opentrv/3d-boxes/src/main/boiler_control_ssr-v0p2_rev1.scad

/*
The OpenTRV project licenses this file to you
under the Apache Licence, Version 2.0 (the "Licence");
you may not use this file except in compliance
with the Licence. You may obtain a copy of the Licence at

http://www.apache.org/licenses/LICENSE-2.0

Unless required by applicable law or agreed to in writing,
software distributed under the Licence is distributed on an
"AS IS" BASIS, WITHOUT WARRANTIES OR CONDITIONS OF ANY
KIND, either express or implied. See the Licence for the
specific language governing permissions and limitations
under the Licence.

Author(s) / Copyright (s): Bo Herrmannsen, Bruno Girin 2013
*/

include <boiler_control_ssr-v0p1_rev1-settings.scad>;
include <common.scad>;
include <bitmap.scad>;


module layer_0_0(thickness=layer_0_0_thickness) {
    difference() {
        box_base(thickness);
        box_mounting_holes(thickness);
        translate([0, box_total_length / 4, 0])
            box_wall_mount_screw_holes(thickness);
        translate([0, 0, -0.1])
            nut_recesses(nut_recess_height);
    }
}

module layer_0_5(thickness=box_layer_thickness) {
    box_spacer_layer(thickness);
}

module layer_0_1b(thickness=layer_0_1b_thickness, hole_offset_z, hole_thickness) {
    difference() {
        box_spacer_layer(thickness);
        
        translate([0, 0, hole_offset_z])
        box_outside_hole(
            wire_hole_controller_side,
            wire_hole_controller_width,
            box_wall_width + 0.1,
            wire_hole_controller_offset,
            hole_thickness
        );
        
    }
}

module layer_0() {
    difference() {
        union() {
            layer_0_0(layer_0_0_thickness);
            translate([0, 0, layer_0_0_thickness - 0.1])
                layer_0_1b(layer_0_1b_thickness, layer_0_1b_hole_offset_z, layer_0_1b_hole_thickness);
        }
        for ( hoffset = [-18 : 6 : 6] ) {
            ventilation_slit(TOP, 2, slit_thickness - 4, box_wall_width, hoffset, slit_offset_z + 2);
        }
        for ( hoffset = [0 : 6 : 18] ) {
            ventilation_slit(BOTTOM, 2, slit_thickness - 4, box_wall_width, hoffset, slit_offset_z + 2);
        }
        for ( hoffset = [-36 : 6 : 36] ) {
            ventilation_slit(RIGHT, 2, slit_thickness - 4, box_wall_width, hoffset, slit_offset_z + 2);
            ventilation_slit(LEFT, 2, slit_thickness - 4, box_wall_width, hoffset, slit_offset_z + 2);
        }
        translate ([
                wire_hole_mains_offset_x,
                -box_total_length / 2 + box_wall_width / 2,
                layer_0_0_thickness + wire_hole_mains_offset_z + wire_hole_mains_radius]) {
            rotate (a = 90, v = [1,0,0])
            cylinder (
                h = box_wall_width + 0.2,
                r=wire_hole_mains_radius,
                $fn=cylinder_resolution, center = true);
        }
    }
    for ( hoffset = [-18 : 6 : 6] ) {
        ventilation_screen(TOP, 4, 1, slit_thickness + 0.1, box_wall_width, 2, hoffset, slit_offset_z - 0.1);
    }
    for ( hoffset = [0 : 6 : 18] ) {
        ventilation_screen(BOTTOM, 4, 1, slit_thickness + 0.1, box_wall_width, 2, hoffset, slit_offset_z - 0.1);
    }
    for ( hoffset = [-36 : 6 : 36] ) {
        ventilation_screen(RIGHT, 4, 1, slit_thickness + 0.1, box_wall_width, 2, hoffset, slit_offset_z - 0.1);
        ventilation_screen(LEFT, 4, 1, slit_thickness + 0.1, box_wall_width, 2, hoffset, slit_offset_z - 0.1);
    }
}


module layer_1() {
    difference() {
        union() {
            difference() {
                box_base(layer_1_thickness);
                box_mounting_holes(layer_1_thickness);
                
                /* SSR label */
                translate([
                    -label_ssr_char_count * 3 * label_block_size,
                    led_hole_radius * 5,
                    layer_1_thickness - label_recess_depth + 0.1
                    ])
                rotate(a = -90, v = [0, 0, 1])
                    8bit_str(label_ssr_chars, label_ssr_char_count, label_block_size, label_recess_depth + 0.1);
                /* OpenTRV label */
                translate([
                    -label_opentrv_char_count * 3.5 * label_block_size,
                    -pcb_length / 4,
                    layer_1_thickness - label_recess_depth + 0.1
                    ])
                rotate(a = -90, v = [0, 0, 1])
                    8bit_str(label_opentrv_chars, label_opentrv_char_count, label_block_size, label_recess_depth + 0.1);
                /* Recesses */
                translate([0, 0, layer_1_thickness - bolt_head_recess_height])
                    nut_recesses(bolt_head_recess_height);

                /* LED hole */
                translate([0, 0, -0.1])
                cylinder (
                    h = layer_1_thickness + 0.2,
                    r = led_hole_radius + hole_fudge_factor,
                    $fn = cylinder_resolution);
            }
        }
        
    }
}

module print_layer(n) {
    if ( n == 0 ) {
        layer_0();
    }
    if ( n == 1 ) {
        layer_1();
    }
}

if(box_layout == BOX_LAYOUT_STACKED) {
    layer_0();

    translate([0, 0, layer_0_thickness + box_layout_spacing])
    layer_1();
}
if(box_layout == BOX_LAYOUT_PRINT) {
    translate([
        -(box_total_width + box_layout_spacing) / 2,
        0,
        0])
    layer_0();

    translate([
         (box_total_width + box_layout_spacing) / 2,
        0,
        0])
    layer_1();
    
    if(use_lilypads == true) {
        lilypads(2, 1, box_total_width, box_total_length);
    }
}
if(box_layout == BOX_LAYOUT_1LAYER_PRINT) {
    for ( dx = [ -(n_prints_x - 1) / 2 : (n_prints_x - 1) / 2 ] ) {
        for ( dy = [ -(n_prints_y - 1) / 2 : (n_prints_y - 1) / 2 ] ) {
            translate([
                dx * (box_total_width + box_layout_spacing),
                dy * (box_total_length + box_layout_spacing),
                0
            ])
            print_layer(layer_to_print);
        }
    }
    
    if(use_lilypads == true) {
        lilypads(n_prints_x, n_prints_y, box_total_width, box_total_length);
    }
}
