opentrv/3d-boxes/src/box_basic.scad

/*
The OpenTRV project licenses this file to you
under the Apache Licence, Version 2.0 (the "Licence");
you may not use this file except in compliance
with the Licence. You may obtain a copy of the Licence at

http://www.apache.org/licenses/LICENSE-2.0

Unless required by applicable law or agreed to in writing,
software distributed under the Licence is distributed on an
"AS IS" BASIS, WITHOUT WARRANTIES OR CONDITIONS OF ANY
KIND, either express or implied. See the Licence for the
specific language governing permissions and limitations
under the Licence.

Author(s) / Copyright (s): Bruno Girin 2013
*/

include <settings.scad>;

box_total_width = pcb_width + 2 * box_wall_width;
box_cube_width = box_total_width - 2 * box_corner_radius;
box_total_length = pcb_length + 2 * box_wall_width;
box_cube_length = box_total_length - 2 * box_corner_radius;
mounting_hole_pcb_offset = pcb_mounting_hole_to_edge + pcb_mounting_hole_radius;
mounting_hole_box_offset = box_wall_width + mounting_hole_pcb_offset;

module box_mounting_hole() {
    translate([0, 0, -0.1])
    cylinder(r = pcb_mounting_hole_radius, h = box_layer_thickness + 0.2);
}

module box_mounting_holes() {
    union() {
        translate([
            -pcb_width / 2 + mounting_hole_pcb_offset,
            -pcb_length / 2 + mounting_hole_pcb_offset,
            0])
        box_mounting_hole();
        translate([
            +pcb_width / 2 - mounting_hole_pcb_offset,
            -pcb_length / 2 + mounting_hole_pcb_offset,
            0])
        box_mounting_hole();
        translate([
            +pcb_width / 2 - mounting_hole_pcb_offset,
            +pcb_length / 2 - mounting_hole_pcb_offset,
            0])
        box_mounting_hole();
        translate([
            -pcb_width / 2 + mounting_hole_pcb_offset,
            +pcb_length / 2 - mounting_hole_pcb_offset,
            0])
        box_mounting_hole();
    }
}

module box_mounting_hole_surround() {
    hull_cube_side = box_layer_thickness - box_corner_radius;
    surround_radius = pcb_mounting_hole_radius + pcb_mounting_hole_max_padding;
    hull() {
        cylinder(r = surround_radius,
            h = box_layer_thickness);
        translate([mounting_hole_pcb_offset, -surround_radius, 0])
            cube(size = [hull_cube_side, hull_cube_side, box_layer_thickness]);
        translate([-surround_radius, mounting_hole_pcb_offset, 0])
            cube(size = [hull_cube_side, hull_cube_side, box_layer_thickness]);
        translate([mounting_hole_pcb_offset, mounting_hole_pcb_offset, 0])
            cube(size = [hull_cube_side, hull_cube_side, box_layer_thickness]);
    }
}

module box_mounting_hole_surrounds() {
    union() {
        translate([
            -pcb_width / 2 + mounting_hole_pcb_offset,
            -pcb_length / 2 + mounting_hole_pcb_offset,
            0])
        rotate(a = 180, v = [0, 0, 1])
        box_mounting_hole_surround();
        translate([
            +pcb_width / 2 - mounting_hole_pcb_offset,
            -pcb_length / 2 + mounting_hole_pcb_offset,
            0])
        rotate(a = -90, v = [0, 0, 1])
        box_mounting_hole_surround();
        translate([
            +pcb_width / 2 - mounting_hole_pcb_offset,
            +pcb_length / 2 - mounting_hole_pcb_offset,
            0])
        box_mounting_hole_surround();
        translate([
            -pcb_width / 2 + mounting_hole_pcb_offset,
            +pcb_length / 2 - mounting_hole_pcb_offset,
            0])
        rotate(a = 90, v = [0, 0, 1])
        box_mounting_hole_surround();
    }
}

module box_base() {
    hull() {
        translate([-box_cube_width / 2, -box_cube_length / 2, 0])
        cylinder(r = box_corner_radius, h = box_layer_thickness);
        translate([+box_cube_width / 2, -box_cube_length / 2, 0])
        cylinder(r = box_corner_radius, h = box_layer_thickness);
        translate([+box_cube_width / 2, +box_cube_length / 2, 0])
        cylinder(r = box_corner_radius, h = box_layer_thickness);
        translate([-box_cube_width / 2, +box_cube_length / 2, 0])
        cylinder(r = box_corner_radius, h = box_layer_thickness);
    }
}

module pcb_hole() {
    translate([-pcb_width / 2, -pcb_length / 2, -0.1])
    cube(size = [pcb_width, pcb_length, box_layer_thickness + 0.2]);
}

module box_inside_tab(side, width, depth, offset) {
    if(side == TOP) {
        translate([offset - width / 2, pcb_length / 2 - depth, 0])
        cube(size = [width, depth, box_layer_thickness]);
    }
    if(side == BOTTOM) {
        translate([offset - width / 2, -pcb_length / 2 - 0.1, 0])
        cube(size = [width, depth + 0.1, box_layer_thickness]);
    }
    if(side == LEFT) {
        translate([-pcb_width / 2 - 0.1, offset - width / 2, 0])
        cube(size = [depth + 0.1, width, box_layer_thickness]);
    }
    if(side == RIGHT) {
        translate([pcb_width / 2 - depth, offset - width / 2, 0])
        cube(size = [depth + 0.1, width, box_layer_thickness]);
    }
}

module box_outside_hole(side, width, depth, offset) {
    if(side == TOP) {
        translate([offset - width / 2, box_total_length / 2 - depth, -0.1])
        cube(size = [width, depth, box_layer_thickness + 0.2]);
    }
    if(side == BOTTOM) {
        translate([offset - width / 2, -box_total_length / 2 - 0.1, -0.1])
        cube(size = [width, depth + 0.1, box_layer_thickness + 0.2]);
    }
    if(side == LEFT) {
        translate([-box_total_width / 2 - 0.1, offset - width / 2, -0.1])
        cube(size = [depth + 0.1, width, box_layer_thickness + 0.2]);
    }
    if(side == RIGHT) {
        translate([box_total_width / 2 - depth, offset - width / 2, -0.1])
        cube(size = [depth + 0.1, width, box_layer_thickness + 0.2]);
    }
}

module box_spacer_layer() {
    difference() {
        union() {
            difference() {
                box_base();
                pcb_hole();
            }
            box_mounting_hole_surrounds();
        }
        box_mounting_holes();
    }
}

module box_layer0() {
    difference() {
        box_base();
        box_mounting_holes();
    }
}

module box_layer1() {
    difference() {
        union() {
            box_spacer_layer();
            box_inside_tab(RIGHT, 7, 3, 9);
            box_inside_tab(RIGHT, 5, 3, -8);
            box_inside_tab(LEFT, 36, 2, 0);
            box_inside_tab(BOTTOM, 6, 3, 16);
            box_inside_tab(BOTTOM, 6, 3, -16);
            box_inside_tab(TOP, 28, 2, 0);
        }
        box_outside_hole(LEFT, 10, box_layer_thickness, -5.5);
    }
}

module box_layer2() {
    difference() {
        box_base();
        pcb_hole();
        box_outside_hole(LEFT, 10, box_layer_thickness + 0.1, -5.5);
    }
}

module box_layer3() {
    difference() {
        union() {
            box_spacer_layer();
            box_inside_tab(LEFT, 10 + 2 * box_layer_thickness, box_layer_thickness, -5.5);
            box_inside_tab(LEFT, 8, 20, -5.5);
        }
        box_outside_hole(LEFT, 10, box_layer_thickness, -5.5);
        box_outside_hole(LEFT, 6, box_layer_thickness + 18, -5.5);
    }
}


translate([0, 0, -15])
box_layer0();

translate([0, 0, -5])
box_layer1();

translate([0, 0, 5])
box_layer2();

translate([0, 0, 15])
box_layer3();
