opentrv/3d-boxes/src/main/box-common.scad

/*
The OpenTRV project licenses this file to you
under the Apache Licence, Version 2.0 (the "Licence");
you may not use this file except in compliance
with the Licence. You may obtain a copy of the Licence at

http://www.apache.org/licenses/LICENSE-2.0

Unless required by applicable law or agreed to in writing,
software distributed under the Licence is distributed on an
"AS IS" BASIS, WITHOUT WARRANTIES OR CONDITIONS OF ANY
KIND, either express or implied. See the Licence for the
specific language governing permissions and limitations
under the Licence.

Author(s) / Copyright (s): Bruno Girin 2013
*/

include <settings.scad>;

/* Calculated values */
box_total_width = pcb_width + 2 * box_wall_width;
box_cube_width = box_total_width - 2 * box_corner_radius;
box_total_length = pcb_length + 2 * box_wall_width;
box_cube_length = box_total_length - 2 * box_corner_radius;
mounting_hole_pcb_offset = pcb_mounting_hole_to_edge + pcb_mounting_hole_radius;
mounting_hole_box_offset = box_wall_width + mounting_hole_pcb_offset;

/* Mounting holes and surrounds */
module box_mounting_hole(thickness=box_layer_thickness) {
    translate([0, 0, -0.1])
    cylinder(
        r = pcb_mounting_hole_radius + hole_fudge_factor,
        h = thickness + 0.2,
        $fn=cylinder_resolution);
}

module box_mounting_holes(thickness=box_layer_thickness) {
    union() {
        translate([
            -pcb_width / 2 + mounting_hole_pcb_offset,
            -pcb_length / 2 + mounting_hole_pcb_offset,
            0])
        box_mounting_hole(thickness);
        translate([
            +pcb_width / 2 - mounting_hole_pcb_offset,
            -pcb_length / 2 + mounting_hole_pcb_offset,
            0])
        box_mounting_hole(thickness);
        translate([
            +pcb_width / 2 - mounting_hole_pcb_offset,
            +pcb_length / 2 - mounting_hole_pcb_offset,
            0])
        box_mounting_hole(thickness);
        translate([
            -pcb_width / 2 + mounting_hole_pcb_offset,
            +pcb_length / 2 - mounting_hole_pcb_offset,
            0])
        box_mounting_hole(thickness);
    }
}

module box_mounting_hole_surround(thickness=box_layer_thickness, extra_padding=0) {
    hull_cube_side = box_wall_width - box_corner_radius;
    surround_radius = pcb_mounting_hole_radius + pcb_mounting_hole_max_padding + extra_padding;
    hull() {
        cylinder(
            r = surround_radius,
            h = thickness,
            $fn=cylinder_resolution);
        translate([mounting_hole_pcb_offset, -surround_radius, 0])
            cube(size = [hull_cube_side, hull_cube_side, thickness]);
        translate([-surround_radius, mounting_hole_pcb_offset, 0])
            cube(size = [hull_cube_side, hull_cube_side, thickness]);
        translate([mounting_hole_pcb_offset, mounting_hole_pcb_offset, 0])
            cube(size = [hull_cube_side, hull_cube_side, thickness]);
    }
}

module box_mounting_hole_surrounds(thickness=box_layer_thickness, extra_padding=0) {
    union() {
        translate([
            -pcb_width / 2 + mounting_hole_pcb_offset,
            -pcb_length / 2 + mounting_hole_pcb_offset,
            0])
        rotate(a = 180, v = [0, 0, 1])
        box_mounting_hole_surround(thickness, extra_padding);
        translate([
            +pcb_width / 2 - mounting_hole_pcb_offset,
            -pcb_length / 2 + mounting_hole_pcb_offset,
            0])
        rotate(a = -90, v = [0, 0, 1])
        box_mounting_hole_surround(thickness, extra_padding);
        translate([
            +pcb_width / 2 - mounting_hole_pcb_offset,
            +pcb_length / 2 - mounting_hole_pcb_offset,
            0])
        box_mounting_hole_surround(thickness, extra_padding);
        translate([
            -pcb_width / 2 + mounting_hole_pcb_offset,
            +pcb_length / 2 - mounting_hole_pcb_offset,
            0])
        rotate(a = 90, v = [0, 0, 1])
        box_mounting_hole_surround(thickness, extra_padding);
    }
}

/* Box base */
module box_base(thickness=box_layer_thickness) {
    hull() {
        translate([-box_cube_width / 2, -box_cube_length / 2, 0])
        cylinder(r = box_corner_radius, h = thickness, $fn=cylinder_resolution);
        translate([+box_cube_width / 2, -box_cube_length / 2, 0])
        cylinder(r = box_corner_radius, h = thickness, $fn=cylinder_resolution);
        translate([+box_cube_width / 2, +box_cube_length / 2, 0])
        cylinder(r = box_corner_radius, h = thickness, $fn=cylinder_resolution);
        translate([-box_cube_width / 2, +box_cube_length / 2, 0])
        cylinder(r = box_corner_radius, h = thickness, $fn=cylinder_resolution);
    }
}

/* PCB hole */
module pcb_hole(thickness=box_layer_thickness, padding=0) {
    translate([-pcb_width / 2 - padding, -pcb_length / 2 - padding, -0.1])
    cube(size = [pcb_width + padding * 2, pcb_length + padding * 2, thickness + 0.2]);
}

/* Generic tabs and holes */
module box_inside_tab(side, width, depth, offset, thickness=box_layer_thickness) {
    if(side == TOP) {
        translate([offset - width / 2, pcb_length / 2 - depth, 0])
        cube(size = [width, depth + 0.1, thickness]);
    }
    if(side == BOTTOM) {
        translate([offset - width / 2, -pcb_length / 2 - 0.1, 0])
        cube(size = [width, depth + 0.1, thickness]);
    }
    if(side == LEFT) {
        translate([-pcb_width / 2 - 0.1, offset - width / 2, 0])
        cube(size = [depth + 0.1, width, thickness]);
    }
    if(side == RIGHT) {
        translate([pcb_width / 2 - depth, offset - width / 2, 0])
        cube(size = [depth + 0.1, width, thickness]);
    }
}

module box_outside_hole(side, width, depth, offset, thickness=box_layer_thickness) {
    if(side == TOP) {
        translate([offset - width / 2, box_total_length / 2 - depth, -0.1])
        cube(size = [width, depth + 0.1, thickness + 0.2]);
    }
    if(side == BOTTOM) {
        translate([offset - width / 2, -box_total_length / 2 - 0.1, -0.1])
        cube(size = [width, depth + 0.1, thickness + 0.2]);
    }
    if(side == LEFT) {
        translate([-box_total_width / 2 - 0.1, offset - width / 2, -0.1])
        cube(size = [depth + 0.1, width, thickness + 0.2]);
    }
    if(side == RIGHT) {
        translate([box_total_width / 2 - depth, offset - width / 2, -0.1])
        cube(size = [depth + 0.1, width, thickness + 0.2]);
    }
}

/* Spacer layer (base layer with PCB hole removed and surrounds added */
module box_spacer_layer(thickness=box_layer_thickness, surround_feet_thickness=0, surround_feet_padding=0) {
    difference() {
        union() {
            difference() {
                box_base(thickness);
                pcb_hole(thickness);
            }
            box_mounting_hole_surrounds(thickness);
            if (surround_feet_thickness > 0) {
                box_mounting_hole_surrounds(surround_feet_thickness, surround_feet_padding);
            }
        }
        box_mounting_holes(thickness);
    }
}

/* Wall mount elements */
module box_wall_mount_screw_hole_shape(thickness, padding=0) {
    translate([0, -pcb_width / 10, -0.1])
        cylinder(
            r = wall_mount_screw_hole_cutout_large_radius + padding,
            h = thickness + 0.2,
            $fn=cylinder_resolution);
    translate([0,  pcb_width / 10, -0.1])
        cylinder(
            r = wall_mount_screw_hole_cutout_radius + padding,
            h = thickness + 0.2,
            $fn=cylinder_resolution);
    translate([
            -wall_mount_screw_hole_cutout_radius - padding, 
            -pcb_width/10,
            -0.1])
        cube(size = [
            (wall_mount_screw_hole_cutout_radius + padding) * 2,
            pcb_width / 5,
            thickness + 0.2]);
}

module box_wall_mount_screw_hole(thickness=box_layer_thickness) {
    union() {
        box_wall_mount_screw_hole_shape(thickness);
        translate([0, 0, thickness - wall_mount_screw_hole_cutout_thickness])
            box_wall_mount_screw_hole_shape(
                wall_mount_screw_hole_cutout_thickness + 0.1,
                wall_mount_screw_hole_cutout_radius * wall_mount_screw_hole_cutout_ratio);
    }
}

module box_wall_mount_screw_holes(thickness=box_layer_thickness) {
    union() {
        translate([-pcb_width * 3 / 10, 0, 0])
            box_wall_mount_screw_hole(thickness);
        translate([ pcb_width * 3 / 10, 0, 0])
            box_wall_mount_screw_hole(thickness);
    }
}

/* Ventilaton slit elements */
module ventilation_slit_core(width, layer_thickness, layer_wall_width) {
    translate([0, 0, layer_thickness / 2])
    cube(size = [width, layer_wall_width + 0.2, layer_thickness - 1], center = true);
}

module ventilation_slit(side, width, layer_thickness, layer_wall_width, hoffset, voffset=0) {
    if(side == TOP) {
        translate([hoffset,  pcb_length / 2 + layer_wall_width / 2, voffset])
        ventilation_slit_core(width, layer_thickness, layer_wall_width);
    }
    if(side == BOTTOM) {
        translate([hoffset, -pcb_length / 2 - layer_wall_width / 2, voffset])
        ventilation_slit_core(width, layer_thickness, layer_wall_width);
    }
    if(side == LEFT) {
        translate([-pcb_width / 2 - layer_wall_width / 2, hoffset, voffset])
        rotate(a = 90, v = [0, 0, 1])
        ventilation_slit_core(width, layer_thickness, layer_wall_width);
    }
    if(side == RIGHT) {
        translate([ pcb_width / 2 + layer_wall_width / 2, hoffset, voffset])
        rotate(a = 90, v = [0, 0, 1])
        ventilation_slit_core(width, layer_thickness, layer_wall_width);
    }
}

/* Ventilation back plate element, only used in stuations where we want to
   protect the inside of the box from any intrusion by foreign objects via
   the ventilation slits. */
module ventilation_screen_core(width, thickness, layer_thickness, strut_length = 0) {
    translate([0, 0, layer_thickness / 2])
    cube(size = [width, thickness, layer_thickness], center = true);
    if (layer_thickness > 5 && strut_length > 0) {
        for ( n = [ 0 : floor(layer_thickness / 5) - 1 ] ) {
            translate([
                0,
                strut_length / 2,
                (layer_thickness - ((floor(layer_thickness / 5) - 1) * 5)) / 2 + n * 5
            ])
            cube(size = [width, thickness + strut_length, 1], center = true);
        }
    }
}

module ventilation_screen(side, width, thickness, layer_thickness, wall_width, screen_offset, hoffset, voffset=0) {
    if(side == TOP) {
        translate([hoffset,  pcb_length / 2 - (screen_offset + thickness), voffset])
        ventilation_screen_core(width, thickness, layer_thickness, wall_width / 2 + thickness / 2 + screen_offset);
    }
    if(side == BOTTOM) {
        translate([hoffset, -pcb_length / 2 + (screen_offset + thickness), voffset])
        rotate(a = 180, v = [0, 0, 1])
        ventilation_screen_core(width, thickness, layer_thickness, wall_width / 2 + thickness / 2 + screen_offset);
    }
    if(side == LEFT) {
        translate([-pcb_width / 2 + (screen_offset + thickness), hoffset, voffset])
        rotate(a = 90, v = [0, 0, 1])
        ventilation_screen_core(width, thickness, layer_thickness, wall_width / 2 + thickness / 2 + screen_offset);
    }
    if(side == RIGHT) {
        translate([ pcb_width / 2 - (screen_offset + thickness), hoffset, voffset])
        rotate(a = -90, v = [0, 0, 1])
        ventilation_screen_core(width, thickness, layer_thickness, wall_width / 2 + thickness / 2 + screen_offset);
    }
}

/* Nut and bolt recesses */
module nut_recess(height) {
    cylinder(
        r = nut_recess_radius,
        h = height + 0.1,
        $fn=cylinder_resolution);
}

module nut_recesses(height) {
    union() {
        translate([
            -pcb_width / 2 + mounting_hole_pcb_offset,
            -pcb_length / 2 + mounting_hole_pcb_offset,
            0])
        nut_recess(height);
        translate([
            +pcb_width / 2 - mounting_hole_pcb_offset,
            -pcb_length / 2 + mounting_hole_pcb_offset,
            0])
        nut_recess(height);
        translate([
            +pcb_width / 2 - mounting_hole_pcb_offset,
            +pcb_length / 2 - mounting_hole_pcb_offset,
            0])
        nut_recess(height);
        translate([
            -pcb_width / 2 + mounting_hole_pcb_offset,
            +pcb_length / 2 - mounting_hole_pcb_offset,
            0])
        nut_recess(height);
    }
}

/* Cylinder to cylinder bridge */
module cylinder_bridge(small_radius, large_radius) {
    /* layer 1 */
    translate([0, 0, (cylinder_bridge_layer_height * 3 + 0.1) / 2])
    difference() {
        cube(size=[large_radius * 2 + 0.2, large_radius * 2 + 0.2, cylinder_bridge_layer_height * 3 + 0.1], center=true);
        cube(size=[small_radius * 2      , large_radius * 2 + 0.2, cylinder_bridge_layer_height * 3 + 0.3], center=true);
    }

    /* layer 2 */
    translate([0, 0, cylinder_bridge_layer_height + ((cylinder_bridge_layer_height * 2 + 0.1) / 2)])
    difference() {
        cube(size=[large_radius * 2 + 0.2, large_radius * 2 + 0.2, cylinder_bridge_layer_height * 2 + 0.1], center=true);
        cube(size=[large_radius * 2 + 0.2, small_radius * 2      , cylinder_bridge_layer_height * 2 + 0.3], center=true);
    }

    /* layer 3 */
    translate([0, 0, 2 * cylinder_bridge_layer_height + ((cylinder_bridge_layer_height + 0.1) / 2)])
    rotate(v=[0, 0, 1], a=45)
    difference() {
        cube(size=[large_radius * 2 + 0.2, large_radius * 2 + 0.2, cylinder_bridge_layer_height + 0.1], center=true);
        cube(size=[small_radius * 2      , small_radius * 2      , cylinder_bridge_layer_height + 0.3], center=true);
    }
}

module cylinder_bridges(small_radius, large_radius) {
    union() {
        translate([
            -pcb_width / 2 + mounting_hole_pcb_offset,
            -pcb_length / 2 + mounting_hole_pcb_offset,
            0])
        cylinder_bridge(small_radius, large_radius);
        translate([
            +pcb_width / 2 - mounting_hole_pcb_offset,
            -pcb_length / 2 + mounting_hole_pcb_offset,
            0])
        cylinder_bridge(small_radius, large_radius);
        translate([
            +pcb_width / 2 - mounting_hole_pcb_offset,
            +pcb_length / 2 - mounting_hole_pcb_offset,
            0])
        cylinder_bridge(small_radius, large_radius);
        translate([
            -pcb_width / 2 + mounting_hole_pcb_offset,
            +pcb_length / 2 - mounting_hole_pcb_offset,
            0])
        cylinder_bridge(small_radius, large_radius);
    }
}

/* Strut shavings for cases where we need to shave off the corner of a
   bolt strut as in the rev1 box.
 */
module strut_shaving(corner, thickness) {
    if(corner == TOP_RIGHT) {
        translate([
            pcb_width / 2 - pcb_mounting_hole_radius - pcb_mounting_hole_to_edge -
                (pcb_mounting_hole_radius + pcb_mounting_hole_max_padding + 0.1),
            pcb_length / 2 - pcb_mounting_hole_radius - pcb_mounting_hole_to_edge -
                (pcb_mounting_hole_radius + pcb_mounting_hole_max_padding + 0.1),
            -0.1])
        cube(size = [
            pcb_mounting_hole_radius + pcb_mounting_hole_max_padding + 0.1,
            pcb_mounting_hole_radius + pcb_mounting_hole_max_padding + 0.1,
            thickness + 0.2]);
    }
    if(corner == TOP_LEFT) {
        translate([
            -pcb_width / 2 + pcb_mounting_hole_radius + pcb_mounting_hole_to_edge,
            pcb_length / 2 - pcb_mounting_hole_radius - pcb_mounting_hole_to_edge -
                (pcb_mounting_hole_radius + pcb_mounting_hole_max_padding + 0.1),
            -0.1])
        cube(size = [
            pcb_mounting_hole_radius + pcb_mounting_hole_max_padding + 0.1,
            pcb_mounting_hole_radius + pcb_mounting_hole_max_padding + 0.1,
            thickness + 0.2]);
    }
    if(corner == BOTTOM_RIGHT) {
        translate([
            pcb_width / 2 - pcb_mounting_hole_radius - pcb_mounting_hole_to_edge -
                (pcb_mounting_hole_radius + pcb_mounting_hole_max_padding + 0.1),
            -pcb_length / 2 + pcb_mounting_hole_radius + pcb_mounting_hole_to_edge,
            -0.1])
        cube(size = [
            pcb_mounting_hole_radius + pcb_mounting_hole_max_padding + 0.1,
            pcb_mounting_hole_radius + pcb_mounting_hole_max_padding + 0.1,
            thickness + 0.2]);
    }
    if(corner == BOTTOM_LEFT) {
        translate([
            -pcb_width / 2 + pcb_mounting_hole_radius + pcb_mounting_hole_to_edge,
            -pcb_length / 2 + pcb_mounting_hole_radius + pcb_mounting_hole_to_edge,
            -0.1])
        cube(size = [
            pcb_mounting_hole_radius + pcb_mounting_hole_max_padding + 0.1,
            pcb_mounting_hole_radius + pcb_mounting_hole_max_padding + 0.1,
            thickness + 0.2]);
    }
}

/* Lilypads */
module lilypad(x, y, rx, ry) {
    translate([x, y, 0])
    scale([1, ry / rx, 1])
    cylinder(h = lilypad_height, r = rx);
}

module lilypad_column(x, rx, ny, box_size_y) {
    /* Start lilypad */
    lilypad(
        x,
        -(ny * box_size_y + (ny - 1) * box_layout_hspacing) / 2,
        rx,
        lilypad_small_radius
    );
    /* Middle lilypads */
    if ( ny > 1) {
        for ( n = [-(ny - 2) / 2 : (ny - 2) / 2] ) {
            lilypad(
                x,
                n * (box_size_y + box_layout_hspacing),
                rx,
                lilypad_large_radius
            );
        }
    }
    /* End lilypad */
    lilypad(
        x,
        (ny * box_size_y + (ny - 1) * box_layout_hspacing) / 2,
        rx,
        lilypad_small_radius
    );
}

module lilypads(nx, ny, box_size_x, box_size_y) {
    /* Start column */
    lilypad_column(
        -(nx * box_size_x + (nx - 1) * box_layout_hspacing) / 2,
        lilypad_small_radius,
        ny,
        box_size_y
    );
    /* Middle columns */
    if ( nx > 1 ) {
        for ( n = [-(nx - 2) / 2 : (nx - 2) / 2] ) {
            lilypad_column(
                n * (box_size_x + box_layout_hspacing),
                lilypad_large_radius,
                ny,
                box_size_y
            );
        }
    }
    /* End column */
    lilypad_column(
        (nx * box_size_x + (nx - 1) * box_layout_hspacing) / 2,
        lilypad_small_radius,
        ny,
        box_size_y
    );
}
